Makerfabs/Project_ESP32-Voice-Interaction/example/ESP32_Interphone/wm8960.h

#include <Wire.h>
#include <FS.h>
#include <SD.h>
#include <Arduino.h>
#include "driver/i2s.h"
#include "Wav.h"
#include "I2S.h"

#define WM8960_ADDRESS 0x1A //AUDIO CODEC ADDRESS

#define LEFT_INPUT_VOLUME 0X00
#define RIGHT_INPUT_VOLUME 0X01
#define LOUT1_VOLUME 0X02
#define ROUT1_VOLUME 0X03
#define CLOCKING_1 0X04
#define ADC_AND_DAC_CONTROL_1 0X05
#define ADC_AND_DAC_CONTROL_2 0X06
#define DIGITAL_AUDIO_INTERFACE 0X07
#define CLOCKING_2 0X08
#define AUDIO_INTERFACE 0X09
#define LEFT_DAC_VOLUME 0X0A
#define RIGHT_DAC_VOLUME 0X0B
#define RESET 0X0F
#define _3D_CONTROL 0X10
#define ALC1 0X11
#define ALC2 0X12
#define ALC3 0X13
#define NOISE_GATE 0X14
#define LEFT_ADC_VOLUME 0X15
#define RIGHT_ADC_VOLUME 0X16
#define ADDITIONAL_CONTROL_1 0X17
#define ADDITIONAL_CONTROL_2 0X18
#define POWER_MANAGEMENT_1 0X19
#define POWER_MANAGEMENT_2 0X1A
#define ADDITIONAL_CONTROL_3 0X1B
#define ANTI_POP_1 0X1C
#define ANTI_POP_2 0X1D
#define ADCL_SIGNAL_PATH 0X20
#define ADCR_SIGNAL_PATH 0X21
#define LEFT_OUT_MIX 0X22
#define RIGHT_OUT_MIX 0X25
#define MONO_OUT_MIX_1 0X26
#define MONO_OUT_MIX_2 0X27
#define LOUT2_VOLUME 0X28
#define ROUT2_VOLUME 0X29
#define MONOOUT_VOLUME 0X2A
#define INPUT_BOOST_MIXER_1 0X2B
#define INPUT_BOOST_MIXER_2 0X2C
#define BYPASS_1 0X2D
#define BYPASS_2 0X2E
#define POWER_MANAGEMENT_3 0X2F
#define ADDITIONAL_CONTROL_4 0X30
#define CLASS_D_CONTROL_1 0X31
#define CLASS_D_CONTROL_3 0X33
#define PLL_N 0X34
#define PLL_K_1 0X35
#define PLL_K_2 0X36
#define PLL_K_3 0X37

uint8_t WM8960_Write_Reg(uint8_t reg, uint16_t dat);

uint8_t WM8960_Init(int DIN, int DOUT, int LRC, int BCLK);

//Only play 16kHz 16bit stereo(2 channel)
void WM8960_Play(String filename, char *buff);

//Only record 16kHz 16bit stereo(2 channel)
void WM8960_Record(String filename, char *buff, int record_time);

// void WM8960_Alarm();

bool WM8960_Volume(float L_volume, float R_volume);

//
void WM8960_Play_psram(uint8_t *buff, int len);
void WM8960_Record_psram(uint8_t *buff, int len);
