Makerfabs/Project_ESP32-Voice-Interaction/example/wav_play/I2S.h

/*
By Vincent
Change for WM8960
16k 16bit stero
*/

#include <Arduino.h>
#include "freertos/FreeRTOS.h"
#include "freertos/task.h"
#include "driver/i2s.h"
#include "esp_system.h"

//#define SAMPLE_RATE (44100)
#define SAMPLE_RATE (16000)
#define DEFAULT_BPS I2S_BITS_PER_SAMPLE_16BIT

#define PIN_I2S_BCLK 26
#define PIN_I2S_LRC 25
#define PIN_I2S_DIN 33
#define PIN_I2S_DOUT 27

/// @parameter MODE : I2S_MODE_RX or I2S_MODE_TX
/// @parameter BPS : I2S_BITS_PER_SAMPLE_16BIT or I2S_BITS_PER_SAMPLE_32BIT
void I2S_Init(int DIN, int DOUT, int LRC, int BCLK);

/// I2S_Read() for I2S_MODE_RX
/// @parameter data: pointer to buffer
/// @parameter numData: buffer size
/// @return Number of bytes read
int I2S_Read(char *data, int numData);

/// I2S_Write() for I2S_MODE_TX
/// @param data: pointer to buffer
/// @param numData: buffer size
void I2S_Write(char *data, int numData);
